dmanojlovic/Senior-Design-Dog-Collar/PCB/Footprints/Boost/Schematic/webench_schematic_exchange_design_18136475_21_Eagle/Eagle/2024-10-11_11-33-58/2024-10-11_11-33-58.sch

## EAGLE design PCB/Footprints/Boost/Schematic/webench_schematic_exchange_design_18136475_21_Eagle/Eagle/2024-10-11_11-33-58/2024-10-11_11-33-58.sch (2024-10-11)

Schematic: 2024-10-11_11-33-58.sch

Parts:
D1: 320mV; M-FLAT
GND: WB_GND
L1: 3.3uH; SLF7045
U1: LM2735XMF/NOPB; MF05A
